tomcombriat/TES_Boelgene/hardware/3D_proto2/jack_support.STL

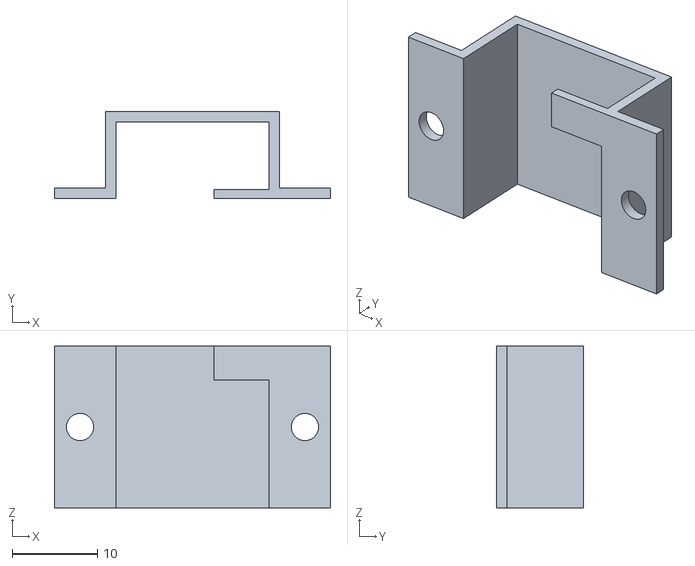
[picture p13: CAD file, 2025-10-06]
hardware/3D_proto2/jack_support.STL
32.4 x 10.2 x 19.0
