tomcombriat/TES_Boelgene/hardware/3D_proto2/cable_holder.STL

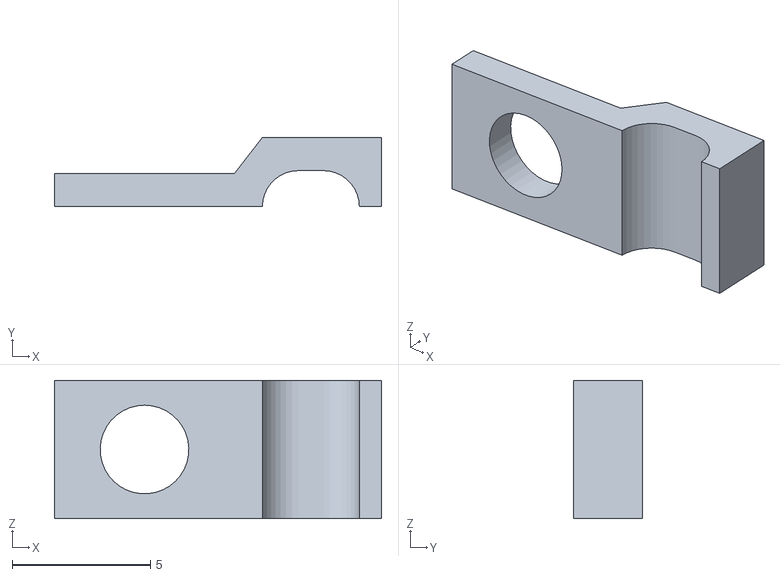
[picture p14: CAD file, 2025-10-06]
hardware/3D_proto2/cable_holder.STL
11.8 x 2.50 x 5.00
