tomcombriat/TES_Boelgene/hardware/3D_proto2/small_idler-Corps.stl

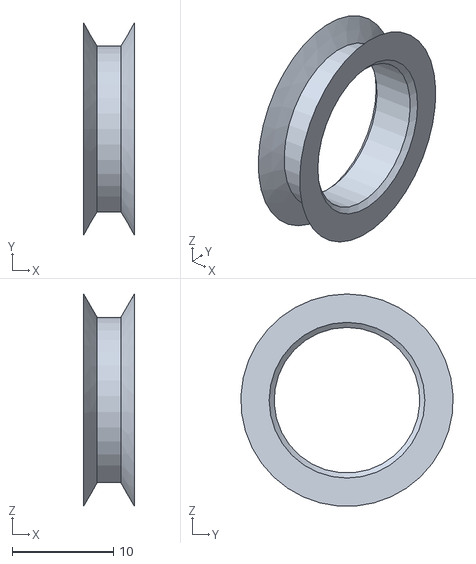
[picture p15: CAD file, 2025-10-06]
hardware/3D_proto2/small_idler-Corps.stl
5.00 x 21.0 x 21.0
