tomcombriat/TES_Boelgene/hardware/3D_proto2/axis_small_idler-Corps.stl

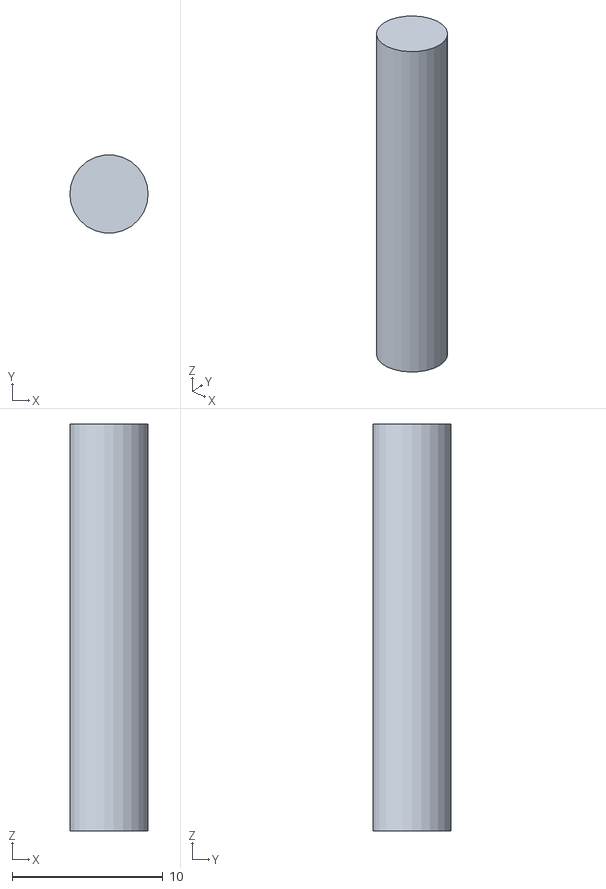
[picture p16: CAD file, 2025-10-06]
hardware/3D_proto2/axis_small_idler-Corps.stl
5.20 x 5.16 x 27.0
