tomcombriat/TES_Boelgene/hardware/3D_proto2/battery_holder.STL

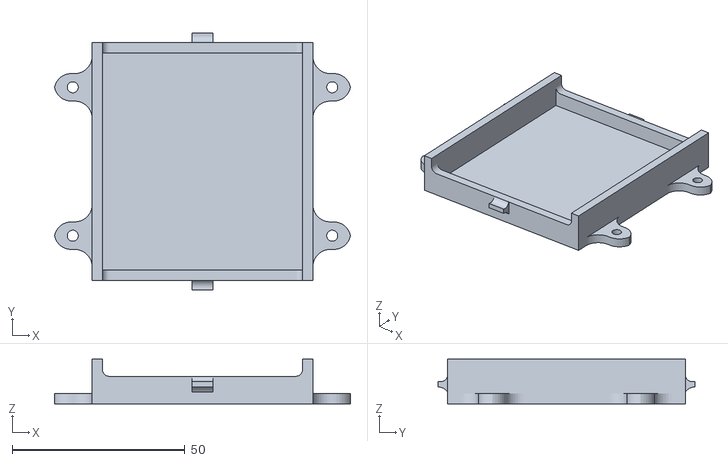
[picture p17: CAD file, 2025-10-06]
hardware/3D_proto2/battery_holder.STL
85.8 x 74.4 x 13.0
