tomcombriat/TES_Boelgene/hardware/3D_proto2/cover_small_idler_holder.FCStd

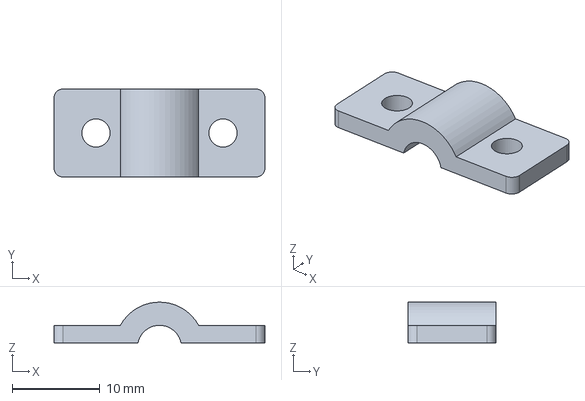
[picture p18: CAD file, 2025-10-06]
hardware/3D_proto2/cover_small_idler_holder.FCStd
24.0 x 10.0 x 4.64 mm
