tomcombriat/TES_Boelgene/hardware/3D_proto2/small_idler_holder.FCStd

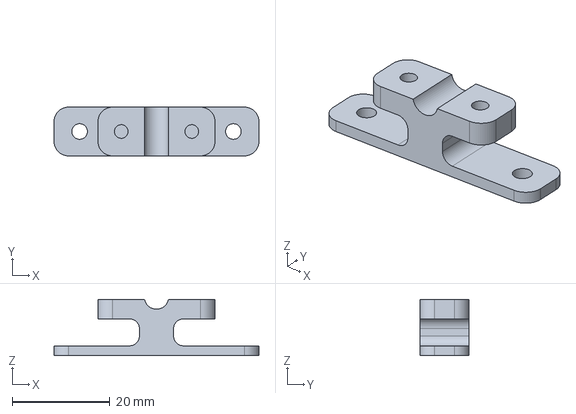
[picture p19: CAD file, 2025-10-06]
hardware/3D_proto2/small_idler_holder.FCStd
42.0 x 10.0 x 11.5 mm
