tomcombriat/TES_Boelgene/hardware/3D_proto2/small_idler_holder-holder.stl

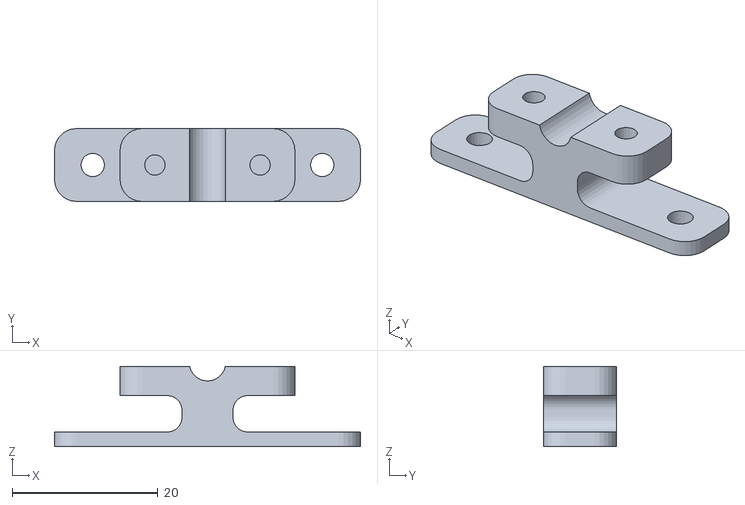
[picture p20: CAD file, 2025-10-06]
hardware/3D_proto2/small_idler_holder-holder.stl
42.0 x 10.0 x 11.0
