tomcombriat/TES_Boelgene/software/FMisNOTdead/modRatioLUT.hpp

#ifndef _MODRATIOLUT_
#define _MODRATIOLUT_

const int8_t RATIO_LUT[256] = {0, 1, 2, 3, 4, 5, 6, 7, 8, 9, 10, 11, 12, 13, 14, 15, 16, 17, 17, 18, 19, 20, 21, 22, 23, 
23, 24, 25, 26, 27, 27, 28, 29, 30, 30, 31, 31, 32, 33, 33, 34, 34, 35, 35, 36, 36, 37, 37, 38, 38, 
38, 39, 39, 39, 40, 40, 40, 40, 40, 40, 41, 41, 41, 41, 41, 41, 41, 41, 41, 40, 40, 40, 40, 40, 40, 
39, 39, 39, 38, 38, 38, 37, 37, 36, 36, 35, 35, 34, 34, 33, 33, 32, 31, 31, 30, 30, 29, 28, 27, 27, 
26, 25, 24, 23, 23, 22, 21, 20, 19, 18, 17, 17, 16, 15, 14, 13, 12, 11, 10, 9, 8, 7, 6, 5, 4, 
3, 2, 1, 0, -1, -2, -3, -4, -5, -6, -7, -8, -9, -10, -11, -12, -13, -14, -15, -16, -17, -17, -18, -19, -20, 
-21, -22, -23, -23, -24, -25, -26, -27, -27, -28, -29, -30, -30, -31, -31, -32, -33, -33, -34, -34, -35, -35, -36, -36, -37, 
-37, -38, -38, -38, -39, -39, -39, -40, -40, -40, -40, -40, -40, -41, -41, -41, -41, -41, -41, -41, -41, -41, -40, -40, -40, 
-40, -40, -40, -39, -39, -39, -38, -38, -38, -37, -37, -36, -36, -35, -35, -34, -34, -33, -33, -32, -31, -31, -30, -30, -29, 
-28, -27, -27, -26, -25, -24, -23, -23, -22, -21, -20, -19, -18, -17, -17, -16, -15, -14, -13, -12, -11, -10, -9, -8, -7, 
-6, -5, -4, -3, -2, -1 };


#endif
